sanjayvdm007-png/DIGITAL-CLOCK/Astable Multivibrator/Astable MultiVibrator using 555 Timer.png

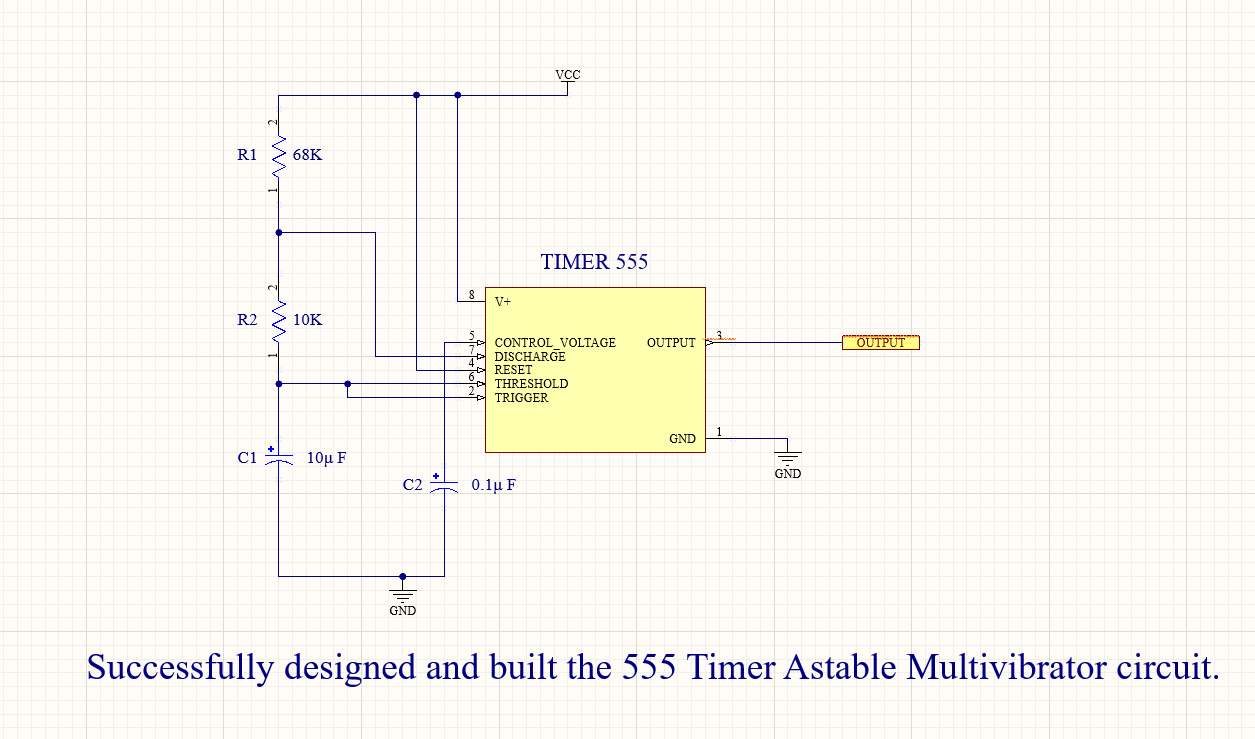
Astable Multivibrator/Astable MultiVibrator using 555 Timer.png
